Indystrycc/OpenScrewCounter/3D printed/wheel nut.3mf

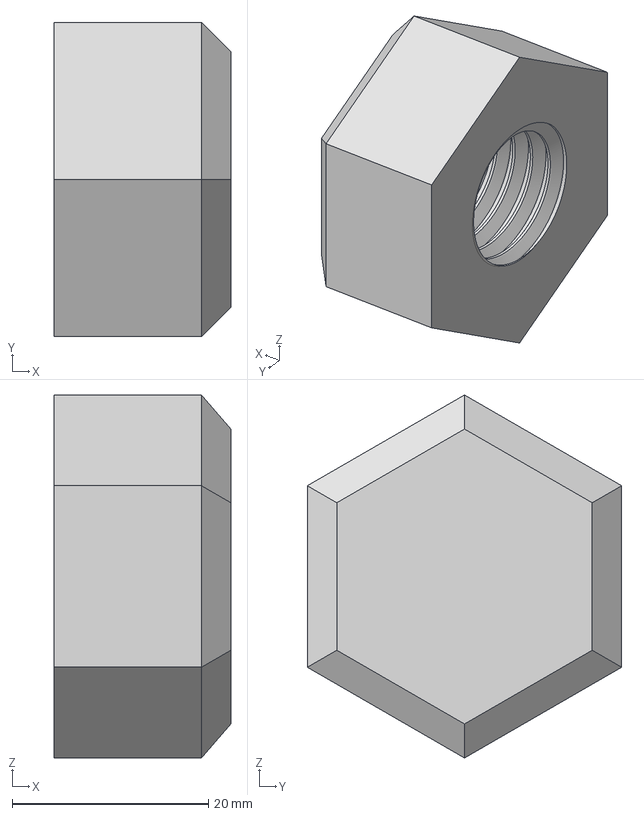
[picture p16: CAD file, 2023-02-21]
3D printed/wheel nut.3mf
18.0 x 32.0 x 37.0 mm
